hairymnstr/oggbox/sch/oggbox.sch

## KiCad design sch/oggbox.sch (2019-10-11, an earlier design)

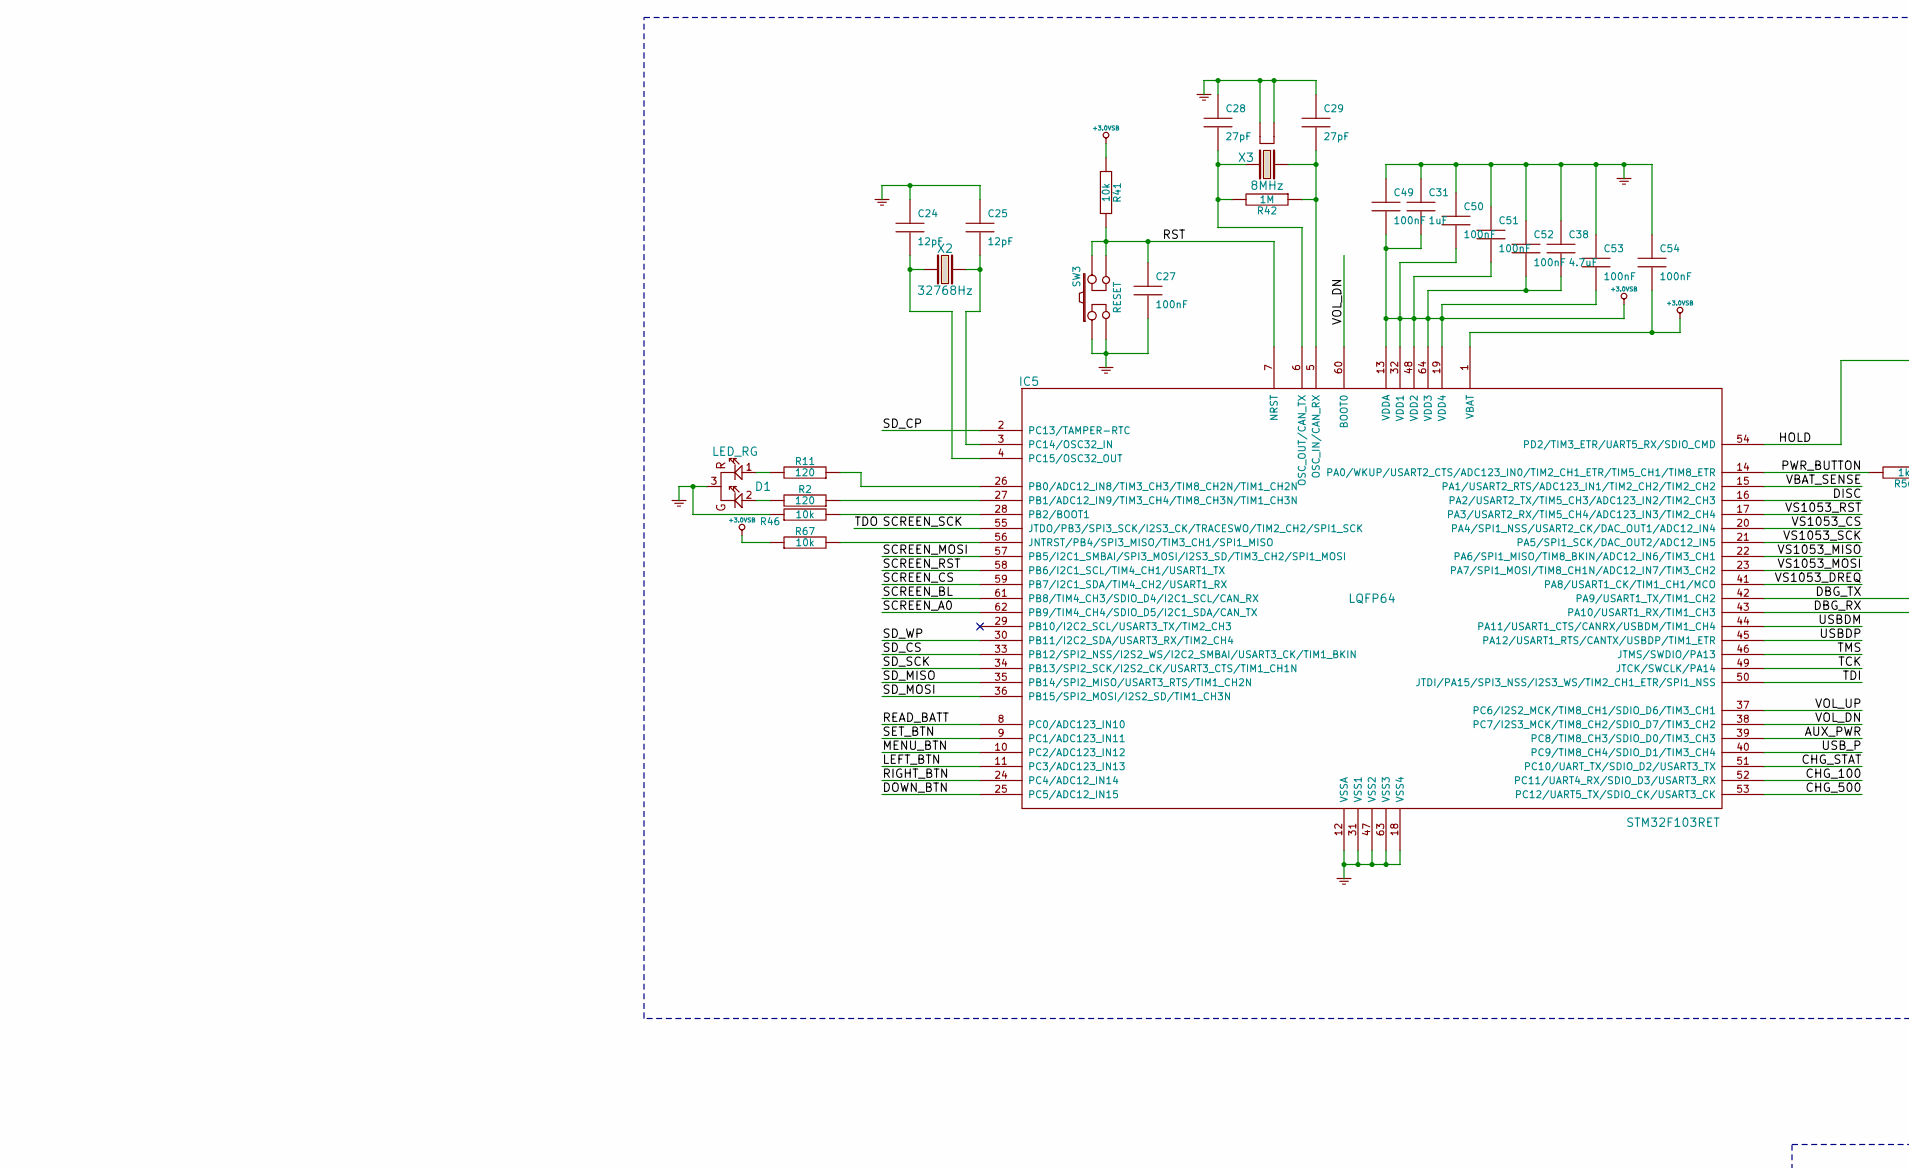
[picture p16: schematic oggbox.sch, part in row 1, column 1]



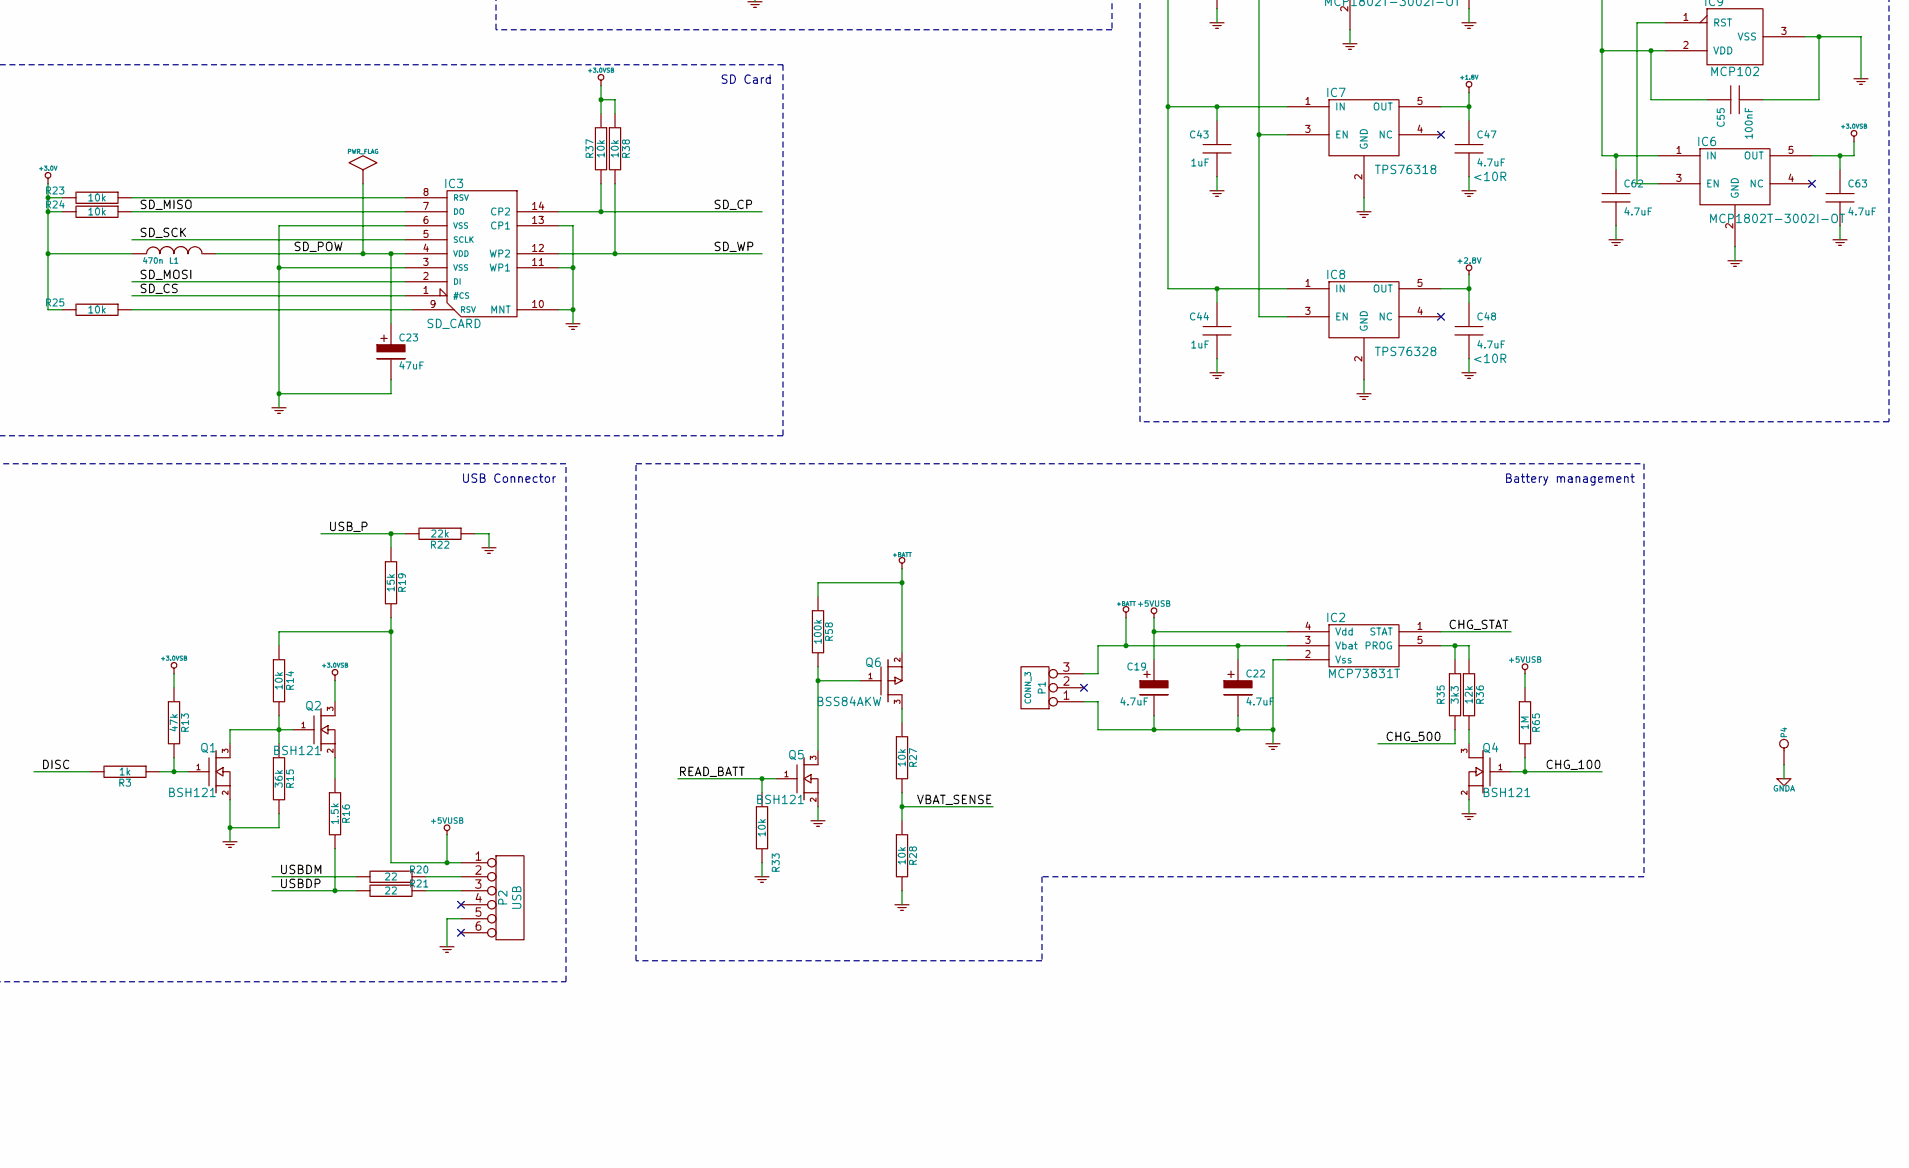
[picture p17: schematic oggbox.sch, part in row 2, column 2]

Parts:
C1, C2: 18pF; SM0603
C3, C4, C7, C31, C43, C44: 1uF; SM0603
C5, C6, C20, C21: 10nF; SM0603
C8, C9, C10, C11, C12, C13, C14, C15, C16, C17, C27, C32, C33, C34, C35, C36, C42, C45, C49, C50, C51, C52, C53, C54, C55, C56, C57, C58, C59, C60, C61: 100nF; SM0603
C18: 47nF; SM0603
C19, C22, C26, C30, C38, C47, C48, C62, C63: 4.7uF; SM0805
C23: 47uF; SM1206
C24, C25: 12pF; SM0603; Tolerance 20%; Voltage 50V
C28, C29: 27pF; SM0603
C37, C39, C40, C41: 2.2uF; SM0805
C46: 100nF; SM0603; Tolerance 20%; Voltage 50V
D1: LED_RG; SOT23
IC1: VS1053; LQFP48
IC2: MCP73831T; SOT23-5
IC3: SD_CARD; SD_UNIVERSAL
IC4, IC6: MCP1802T-3002I-OT; SOT23-5
IC5: STM32F103RET; LQFP64
IC7: TPS76318; SOT23-5
IC8: TPS76328; SOT23-5
IC9: MCP102; SOT23
L1: 470n; SM1206
P1: CONN_3; JST_S3B_XHA
P2: USB; MICRO_USB_1568026
P3: CORTEX DEBUG; SAMTEC_SHF-SM_5x2
P4: CONN_1
P5: CONN_4; BTHQ128064AVD1
P6: CONN_28; AMP_FPC_28_05MM
P7: FTDI; HEADER_6
P9: LINE; JACK_LUMBERG_1503_13_VP3
P10: PHONES; JACK_LUMBERG_1503_13_VP3
Q1, Q2, Q3, Q4, Q5: BSH121; SOT323
Q6: BSS84AKW; SOT323
R1, R4, R5, R6, R7, R8, R9, R10, R14, R23, R24, R25, R26, R27, R28, R33, R37, R38, R40, R43, R47, R55: 10k; SM0603
R2, R11: 120; SM0603; Tolerance 5%
R3, R32, R34, R44, R48, R59, R60, R61: 1k; SM0603
R12, R42, R65: 1M; SM0603
R13: 47k; SM0603
R15: 36k; SM0603
R16: 1.5k; SM0603
R17, R18: 470; SM0603
R19: 15k; SM0603
R20, R21, R29, R30, R31, R45, R53, R54: 22; SM0603
R22: 22k; SM0603
R35: 3k3; SM0603
R36: 12k; SM0603
R39: 0; SM0603
R41, R46, R67: 10k; SM0603; Tolerance 5%
R49, R50, R51, R52, R58, R62, R63, R64, R66: 100k; SM0603
R56: 1k; SM0603; Tolerance 5%
R57: 22k; SM0603; Tolerance 5%
SW1: VOL_UP; SW_SKQLLCE012
SW2: VOL_DN; SW_SKQLLCE012
SW3: RESET; SW_SKQLLCE012
SW4: MENU; SW_EVQQ2P03W
SW5: SET; SW_EVQQ2P03W
SW7: DOWN; SW_EVQQ2P03W
SW8: LEFT; SW_EVQQ2P03W
SW9: RIGHT; SW_EVQQ2P03W
SW10: UP; SW_EVQQ2P03W
SW11: HOLD; PCM12SMTR
X1: 12.288MHz; CRYSTAL-SMD-5-3_2
X2: 32768Hz; MC306
X3: 8MHz; CRYSTAL-SMD-5-3_2

Connections:
+1.8V: C14.2, C15.2, C16.2, C17.2, C47.1, IC1.5 (CVDD0), IC1.7 (CVDD1), IC1.24 (CVDD2), IC1.31 (CVDD3), IC7.5 (OUT)
+2.8V: C8.2, C9.2, C10.2, C48.1, IC1.38 (AVDD0), IC1.43 (AVDD1), IC1.45 (AVDD2), IC8.5 (OUT)
+3.0V: C11.2, C12.2, C13.2, C30.1, C42.1, C45.1, C56.1, C57.1, C58.1, C59.1, C60.1, C61.1, IC1.6 (IOVDD0), IC1.14 (IOVDD1), IC1.19 (IOVDD2), IC1.32 (XTEST), IC4.5 (OUT), L1.1, P6.15, R10.1, R23.2, R24.2, R25.2, R26.1, R53.2, R54.2, SW1.1, SW1.3, SW2.1, SW2.3, SW4.1, SW4.3, SW5.1, SW5.3, SW7.1, SW7.3, SW8.1, SW8.3, SW9.1, SW9.3
+3.0VSB: C31.2, C38.2, C49.2, C50.2, C51.2, C52.2, C53.2, C54.2, C63.1, IC5.1 (VBAT), IC5.13 (VDDA), IC5.19 (VDD4), IC5.32 (VDD1), IC5.48 (VDD2), IC5.64 (VDD3), IC6.5 (OUT), P3.1, Q2.3 (D), R13.1, R37.1, R38.1, R41.1, R67.1, SW11.1
+5VUSB: C19.1, IC2.4 (Vdd), P2.1, R14.1, R19.2, R65.1
+BATT: C22.1, C26.1, C43.1, C44.1, C55.1, C62.1, IC2.3 (Vbat), IC4.1 (IN), IC6.1 (IN), IC7.1 (IN), IC8.1 (IN), IC9.2 (VDD), P1.3, Q6.2 (S), R58.1
A1: P5.1, R53.1
A2: P5.3, R54.1
AUX_PWR: IC4.3 (EN), IC5.39 (PC8/TIM8_CH3/SDIO_D0/TIM3_CH3), IC7.3 (EN), IC8.3 (EN), R66.1
CHG_100: IC5.52 (PC11/UART4_RX/SDIO_D3/USART3_RX), Q4.1 (G), R65.2
CHG_500: IC5.53 (PC12/UART5_TX/SDIO_CK/USART3_CK), R35.2
CHG_STAT: IC2.1 (STAT), IC5.51 (PC10/UART_TX/SDIO_D2/USART3_TX)
DBG_RX: IC5.43 (PA10/USART1_RX/TIM1_CH3), P7.4
DBG_TX: IC5.42 (PA9/USART1_TX/TIM1_CH2), P7.5
DISC: IC5.16 (PA2/USART2_TX/TIM5_CH3/ADC123_IN2/TIM2_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), R3.2
DOWN_BTN: IC5.25 (PC5/ADC12_IN15), R34.1
GND: C1.2, C2.2, C11.1, C12.1, C13.1, C14.1, C15.1, C16.1, C17.1, C19.2, C22.2, C23.2, C24.1, C25.1, C26.2, C27.2, C28.1, C29.1, C30.2, C31.1, C32.2, C33.2, C34.2, C35.2, C36.2, C38.1, C41.2, C42.2, C43.2, C44.2, C47.2, C48.2, C49.1, C50.1, C51.1, C52.1, C53.1, C54.1, C55.2, C62.2, C63.2, D1.3 (GND), IC1.4 (DGND0), IC1.16 (DGND1), IC1.20 (DGND2), IC1.21 (DGND3), IC1.22 (DGND4), IC1.35 (GND), IC2.2 (Vss), IC3.3 (VSS), IC3.6 (VSS), IC3.10 (MNT), IC3.11 (WP1), IC3.13 (CP1), IC4.2 (GND), IC5.12 (VSSA), IC5.18 (VSS4), IC5.31 (VSS1), IC5.47 (VSS2), IC5.63 (VSS3), IC6.2 (GND), IC7.2 (GND), IC8.2 (GND), IC9.3 (VSS), P1.1, P2.5, P3.3, P3.5, P3.9, P6.1, P6.2, P6.14, P7.1, P7.2, Q1.2 (S), Q3.2 (S), Q4.2 (S), Q5.2 (S), R1.2, R4.2, R5.2, R6.2, R7.2, R8.2, R9.2, R15.2, R22.1, R28.2, R33.2, R39.2, R40.2, R43.2, R46.1, R47.2, R49.1, R50.2, R51.2, R52.2, R55.2, R57.1, R62.2, R63.1, R64.2, R66.2, SW3.1, SW3.3, SW11.3, SW11.4 (MECH), X1.2 (GND), X1.4 (GND), X3.2 (GND), X3.4 (GND)
GNDA: C5.1, C6.1, C7.2, C8.1, C9.1, C10.1, C18.2, C20.2, C21.2, IC1.37 (AGND0), IC1.40 (AGND1), IC1.41 (AGND2), IC1.47 (AGND3), P4.1, P9.1, R39.1
HOLD: C46.1, IC5.54 (PD2/TIM3_ETR/UART5_RX/SDIO_CMD), SW10.1, SW10.3, SW11.2
K: P5.2, P5.4, Q3.3 (D)
LEFT_BTN: IC5.11 (PC3/ADC123_IN13), R44.1
MENU_BTN: IC5.10 (PC2/ADC123_IN12), R32.1
unnamed: C1.1, IC1.17 (XTALO), R12.1, X1.1
unnamed: C2.1, IC1.18 (XTALI), R12.2, X1.3
unnamed: C3.1, R17.2
unnamed: C3.2, P9.4b
unnamed: C4.1, R18.2
unnamed: C4.2, P9.3
unnamed: C5.2, IC1.1 (MICP/LINE1), R17.1
unnamed: C6.2, IC1.48 (LINE2), R18.1
unnamed: C7.1, IC1.44 (RCAP)
unnamed: C18.1, R29.2, R45.2
unnamed: C20.1, R30.2
unnamed: C21.1, R31.2
unnamed: C24.2, IC5.4 (PC15/OSC32_OUT), X2.2
unnamed: C25.2, IC5.3 (PC14/OSC32_IN), X2.1
unnamed: C28.2, IC5.6 (OSC_OUT/CAN_TX), R42.2, X3.3
unnamed: C29.2, IC5.5 (OSC_IN/CAN_RX), R42.1, X3.1
unnamed: C32.1, P6.3
unnamed: C33.1, P6.4
unnamed: C34.1, P6.5
unnamed: C35.1, P6.6
unnamed: C36.1, P6.7
unnamed: C37.1, P6.8
unnamed: C37.2, P6.9
unnamed: C39.1, P6.10
unnamed: C39.2, C40.2, P6.11
unnamed: C40.1, P6.12
unnamed: C41.1, P6.13
unnamed: C45.2, R32.2, R49.2, SW4.2, SW4.4
unnamed: C46.2, R56.1, R57.2, SW10.4
unnamed: C56.2, R34.2, R50.1, SW7.2, SW7.4
unnamed: C57.2, R44.2, R51.1, SW8.2, SW8.4
unnamed: C58.2, R48.2, R52.1, SW9.2, SW9.4
unnamed: C59.2, R59.2, R62.1, SW5.2, SW5.4
unnamed: D1.1 (RED), R11.2
unnamed: D1.2 (GRN), R2.2
unnamed: IC1.9 (GPIO2/DCLK), R6.1
unnamed: IC1.10 (GPIO3/SDATA), R7.1
unnamed: IC1.11 (GPIO6/I2S_SCLK), R40.1
unnamed: IC1.12 (GPIO7/I2S_SDATA), R43.1
unnamed: IC1.13 (XDCS/BSYNC), R10.2
unnamed: IC1.25 (GPIO5/I2S_MCLK), R9.1
unnamed: IC1.26 (RX), R26.2
unnamed: IC1.33 (GPIO0), R4.1
unnamed: IC1.34 (GPIO1), R5.1
unnamed: IC1.36 (GPIO4/I2S_LROUT), R8.1
unnamed: IC1.39 (RIGHT), P10.3, R30.1
unnamed: IC1.42 (GBUF), P10.1, R29.1, R45.1
unnamed: IC1.46 (LEFT), P10.4a, P10.4b, R31.1
unnamed: IC2.5 (PROG), R35.1, R36.1
unnamed: IC3.8 (RSV), R23.1
unnamed: IC3.9 (RSV), R25.1
unnamed: IC5.26 (PB0/ADC12_IN8/TIM3_CH3/TIM8_CH2N/TIM1_C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), R11.1
unnamed: IC5.27 (PB1/ADC12_IN9/TIM3_CH4/TIM8_CH3N/TIM1_C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), R2.1
unnamed: IC5.28 (PB2/BOOT1), R46.2
unnamed: IC5.56 (JNTRST/PB4/SPI3_MISO/TIM3_CH1/SPI1_MISO), R67.2
unnamed: IC6.3 (EN), IC9.1 (RST)
unnamed: P2.2, R20.1
unnamed: P2.3, R21.1
unnamed: Q1.1 (G), R3.1, R13.2
unnamed: Q1.3 (D), Q2.1 (G), R14.2, R15.1
unnamed: Q2.2 (S), R16.1
unnamed: Q4.3 (D), R36.2
unnamed: Q5.3 (D), Q6.1 (G), R58.2
unnamed: Q6.3 (D), R27.1
PWR_BUTTON: IC5.14 (PA0/WKUP/USART2_CTS/ADC123_IN0/TIM2_CH1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), R56.2
READ_BATT: IC5.8 (PC0/ADC123_IN10), Q5.1 (G), R33.1
RIGHT_BTN: IC5.24 (PC4/ADC12_IN14), R48.1
RST: C27.1, IC5.7 (NRST), P3.10, R41.2, SW3.2, SW3.4
SCREEN_A0: IC5.62 (PB9/TIM4_CH4/SDIO_D5/I2C1_SDA/CAN_TX), P6.26
SCREEN_BL: IC5.61 (PB8/TIM4_CH3/SDIO_D4/I2C1_SCL/CAN_RX), Q3.1 (G), R47.1
SCREEN_CS: IC5.59 (PB7/I2C1_SDA/TIM4_CH2/USART1_RX), P6.27
SCREEN_MOSI: IC5.57 (PB5/I2C1_SMBAI/SPI3_MOSI/I2S3_SD/TIM3_C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), P6.16
SCREEN_RST: IC5.58 (PB6/I2C1_SCL/TIM4_CH1/USART1_TX), P6.28, R55.1
SCREEN_SCK: IC5.55 (JTDO/PB3/SPI3_SCK/I2S3_CK/TRACESWO/TIM2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), P3.6, P6.17
SD_CP: IC3.14 (CP2), IC5.2 (PC13/TAMPER-RTC), R37.2
SD_CS: IC3.1 (#CS), IC5.33 (PB12/SPI2_NSS/I2S2_WS/I2C2_SMBAI/USART3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)
SD_MISO: IC3.7 (DO), IC5.35 (PB14/SPI2_MISO/USART3_RTS/TIM1_CH2N), R24.1
SD_MOSI: IC3.2 (DI), IC5.36 (PB15/SPI2_MOSI/I2S2_SD/TIM1_CH3N)
SD_POW: C23.1, IC3.4 (VDD), L1.2
SD_SCK: IC3.5 (SCLK), IC5.34 (PB13/SPI2_SCK/I2S2_CK/USART3_CTS/TIM1_C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)
SD_WP: IC3.12 (WP2), IC5.30 (PB11/I2C2_SDA/USART3_RX/TIM2_CH4), R38.2
SET_BTN: IC5.9 (PC1/ADC123_IN11), R59.1
TCK: IC5.49 (JTCK/SWCLK/PA14), P3.4
TDI: IC5.50 (JTDI/PA15/SPI3_NSS/I2S3_WS/TIM2_CH1_ETR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), P3.8
TMS: IC5.46 (JTMS/SWDIO/PA13), P3.2
USBDM: IC5.44 (PA11/USART1_CTS/CANRX/USBDM/TIM1_CH4), R20.2
USBDP: IC5.45 (PA12/USART1_RTS/CANTX/USBDP/TIM1_ETR), R16.2, R21.2
USB_P: IC5.40 (PC9/TIM8_CH4/SDIO_D1/TIM3_CH4), R19.1, R22.2
VBAT_SENSE: IC5.15 (PA1/USART2_RTS/ADC123_IN1/TIM2_CH2/TIM2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), R27.2, R28.1
VDNB: C61.2, R61.1, R64.1, SW2.2, SW2.4
VOL_DN: IC5.38 (PC7/I2S3_MCK/TIM8_CH2/SDIO_D7/TIM3_CH2), IC5.60 (BOOT0), R61.2
VOL_UP: IC5.37 (PC6/I2S2_MCK/TIM8_CH1/SDIO_D6/TIM3_CH1), R60.1
VS1053_CS: IC1.23 (XCS), IC5.20 (PA4/SPI1_NSS/USART2_CK/DAC_OUT1/ADC12_I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)
VS1053_DREQ: IC1.8 (DREQ), IC5.41 (PA8/USART1_CK/TIM1_CH1/MCO)
VS1053_MISO: IC1.30 (SO), IC5.22 (PA6/SPI1_MISO/TIM8_BKIN/ADC12_IN6/TIM3_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)
VS1053_MOSI: IC1.29 (SI), IC5.23 (PA7/SPI1_MOSI/TIM8_CH1N/ADC12_IN7/TIM3_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)
VS1053_RST: IC1.3 (XRESET), IC5.17 (PA3/USART2_RX/TIM5_CH4/ADC123_IN3/TIM2_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), R1.1
VS1053_SCK: IC1.28 (SCLK), IC5.21 (PA5/SPI1_SCK/DAC_OUT2/ADC12_IN5)
VUPB: C60.2, R60.2, R63.2, SW1.2, SW1.4

Notes on the sheet:
CODEC Chip
SD Card
USB Connector
Battery management
Power Supply
Screen
Buttons
Processor
