hairymnstr/oggbox/src/firmware/ob_screen.c

#include <libopenstm32/gpio.h>
#include <libopenstm32/timer.h>
#include <libopenstm32/rcc.h>
#include "config.h"
#include "ob_screen.h"

int screen_row, screen_col, screen_inv, screen_top_row;

extern char *font[];

void ob_screen_setup() {

  rcc_peripheral_enable_clock(&RCC_APB2ENR, RCC_APB2ENR_TIM1EN);
  rcc_peripheral_enable_clock(&RCC_APB2ENR, RCC_APB2ENR_IOPAEN | RCC_APB2ENR_AFIOEN);
  rcc_peripheral_enable_clock(&RCC_APB2ENR, RCC_APB2ENR_IOPCEN);
  rcc_peripheral_enable_clock(&RCC_APB2ENR, RCC_APB2ENR_IOPDEN);
  /* === setup GPIO === */
   /* PWM output for backlight brightness */
  gpio_set_mode(SCREEN_BL_PORT, GPIO_MODE_OUTPUT_50_MHZ,
                GPIO_CNF_OUTPUT_ALTFN_PUSHPULL, SCREEN_BL);

   /* CS output for contrast control */
  gpio_set_mode(SCREEN_CON_PORT, GPIO_MODE_OUTPUT_50_MHZ,
                GPIO_CNF_OUTPUT_PUSHPULL, SCREEN_CON);
  gpio_set(SCREEN_CON_PORT, SCREEN_CON);  /* de-select this chip normally */

   /* Reset line */
  gpio_set_mode(SCREEN_RST_PORT, GPIO_MODE_OUTPUT_50_MHZ,
                GPIO_CNF_OUTPUT_PUSHPULL, SCREEN_RST);
  gpio_clear(SCREEN_RST_PORT, SCREEN_RST);    /* put chip in reset to start with */

   /* Chip selects, enable, r/w and d/i */
  gpio_set_mode(SCREEN_CS1_PORT, GPIO_MODE_OUTPUT_50_MHZ,
                GPIO_CNF_OUTPUT_PUSHPULL, SCREEN_CS1);
  gpio_set_mode(SCREEN_CS2_PORT, GPIO_MODE_OUTPUT_50_MHZ,
                GPIO_CNF_OUTPUT_PUSHPULL, SCREEN_CS2);
  gpio_set_mode(SCREEN_E_PORT, GPIO_MODE_OUTPUT_50_MHZ,
                GPIO_CNF_OUTPUT_PUSHPULL, SCREEN_E);
  gpio_set_mode(SCREEN_DI_PORT, GPIO_MODE_OUTPUT_50_MHZ,
                GPIO_CNF_OUTPUT_PUSHPULL, SCREEN_DI);
  gpio_set_mode(SCREEN_RW_PORT, GPIO_MODE_OUTPUT_50_MHZ,
                GPIO_CNF_OUTPUT_PUSHPULL, SCREEN_RW);

   /* leave the actual data bus floating for now, will set dir later */

  /* === Setup PWM peripherals for brightness === */
   /* global settings for timer 1 */
  TIM1_CR1 = TIM_CR1_CKD_CK_INT | TIM_CR1_CMS_EDGE;
  TIM1_ARR = 65535;
  TIM1_PSC = 0;
  TIM1_EGR = TIM_EGR_UG;

   /* timer 1 channel 2 (screen brightness) */
  TIM1_CCMR1 |= TIM_CCMR1_OC2M_PWM1 | TIM_CCMR1_OC2PE;
  TIM1_CCER |= TIM_CCER_CC2E;
  TIM1_CCR2 = 0;

  TIM1_CR1 |= TIM_CR1_ARPE;
  TIM1_CR1 |= TIM_CR1_CEN;

  TIM1_BDTR |= TIM_BDTR_MOE;

}

void ob_screen_set_bl(unsigned short level) {
/*  if(level > 127) {
    gpio_set(SCREEN_BL_PORT, SCREEN_BL);
  } else {
    gpio_clear(SCREEN_BL_PORT, SCREEN_BL);
  }*/

  TIM1_CCR2 = level;

  return;
}

void ob_screen_set_contrast(unsigned short level) {
  /* TODO: put a mutex to avoid interfering with screen select?? */
  int temp_cs=0;
  register int i, j;
  /* save chip selects */
  if(gpio_get(SCREEN_CS1_PORT, SCREEN_CS1)) {
    temp_cs |= 1;
    gpio_clear(SCREEN_CS1_PORT, SCREEN_CS1);
  }
  if(gpio_get(SCREEN_CS2_PORT, SCREEN_CS2)) {
    temp_cs |= 2;
    gpio_clear(SCREEN_CS2_PORT, SCREEN_CS2);
  }

  gpio_set_mode(SCREEN_DATA_PORT, GPIO_MODE_OUTPUT_50_MHZ,
                GPIO_CNF_OUTPUT_PUSHPULL, 0x3);
  
  level = (level >> 8) & 0xFF;

  level = level | 0x1100;   /* write value to pot 0 */

  gpio_clear(SCREEN_DATA_PORT, 0);    /* clock starts low */

  if(level & 0x8000) {
    gpio_set(SCREEN_DATA_PORT, 1);
  } else {
    gpio_clear(SCREEN_DATA_PORT, 1);
  }

  gpio_clear(SCREEN_CON_PORT, SCREEN_CON);  /* activate chip select */

  for(i=14;i>=0;i--) {
    for(j=0;j<5;j++);
    gpio_set(SCREEN_DATA_PORT, 0);    /* clock high, latches data */
    for(j=0;j<4;j++);
    if(level & (1 << i)) {
      gpio_set(SCREEN_DATA_PORT, 1);
    } else {
      gpio_clear(SCREEN_DATA_PORT, 1);
    }
    gpio_clear(SCREEN_DATA_PORT, 0);  /* clock low again */
  }
  /* need to put final clock pulse out, last data bit is already on the bus */
  for(j=0;j<5;j++);
  gpio_set(SCREEN_DATA_PORT, 0);
  for(j=0;j<5;j++);
  gpio_clear(SCREEN_DATA_PORT, 0);

  /* clear the CS */
  gpio_set(SCREEN_CON_PORT, SCREEN_CON);

  /* reset the data bus to input */
  gpio_set_mode(SCREEN_DATA_PORT, GPIO_MODE_INPUT,
                GPIO_CNF_INPUT_FLOAT, 0x3);

  /* replace chip select lines */
  if(temp_cs & 1) {
    gpio_set(SCREEN_CS1_PORT, SCREEN_CS1);
  }
  if(temp_cs & 2) {
    gpio_set(SCREEN_CS2_PORT, SCREEN_CS2);
  }
    
  return;
}

void ob_screen_instruction(unsigned char code, unsigned char val) {
  int i, t;

  /* instruction mode */
  gpio_clear(SCREEN_DI_PORT, SCREEN_DI);
  /* read mode */
  gpio_set(SCREEN_RW_PORT, SCREEN_RW);
  
  /* wait for screen to be ready */
  do {
    for(i=0;i<WAIT;i++);
    gpio_set(SCREEN_E_PORT, SCREEN_E);
    for(i=0;i<WAIT;i++);
    t = SCREEN_DATA_IN & 0x80;     /* mask for the busy flag */
    gpio_clear(SCREEN_E_PORT, SCREEN_E);
  } while(t);

  /* set write mode */
  gpio_clear(SCREEN_RW_PORT, SCREEN_RW);

  /* set the data bus to write */
  gpio_set_mode(SCREEN_DATA_PORT, GPIO_MODE_OUTPUT_50_MHZ,
                GPIO_CNF_OUTPUT_PUSHPULL, 0xFF);

  for(i=0;i<WAIT;i++);

  SCREEN_DATA_OUT = (SCREEN_DATA_OUT & 0xFF00) | code | val;

  for(i=0;i<WAIT;i++);
  gpio_set(SCREEN_E_PORT, SCREEN_E);
  for(i=0;i<WAIT;i++);
  gpio_clear(SCREEN_E_PORT, SCREEN_E);

  for(i=0;i<WAIT;i++);
  /* set the data bus back to input only */
  gpio_set_mode(SCREEN_DATA_PORT, GPIO_MODE_INPUT,
                GPIO_CNF_INPUT_FLOAT, 0xFF);

  return;
}

void ob_screen_data(unsigned char val) {
  int i, t;

  /* instruction mode */
  gpio_clear(SCREEN_DI_PORT, SCREEN_DI);
  /* read mode */
  gpio_set(SCREEN_RW_PORT, SCREEN_RW);
  
  //ob_printf("checking screen status\n");

  /* wait for screen to be ready */
  do {
    for(i=0;i<WAIT;i++);
    gpio_set(SCREEN_E_PORT, SCREEN_E);
    for(i=0;i<WAIT;i++);
    t = SCREEN_DATA_IN & 0x80;     /* mask for the busy flag */
    //ob_printf("data is %x\n", SCREEN_DATA_IN);
    gpio_clear(SCREEN_E_PORT, SCREEN_E);
  } while(t);

  //ob_printf("okay, writing data\n");

  /* set write mode */
  gpio_clear(SCREEN_RW_PORT, SCREEN_RW);
  /* data mode */
  gpio_set(SCREEN_DI_PORT, SCREEN_DI);

  /* set the data bus to write */
  gpio_set_mode(SCREEN_DATA_PORT, GPIO_MODE_OUTPUT_50_MHZ,
                GPIO_CNF_OUTPUT_PUSHPULL, 0xFF);

  for(i=0;i<WAIT;i++);

  SCREEN_DATA_OUT = (SCREEN_DATA_OUT & 0xFF00) | val;

  for(i=0;i<WAIT;i++);
  gpio_set(SCREEN_E_PORT, SCREEN_E);
  for(i=0;i<WAIT;i++);
  gpio_clear(SCREEN_E_PORT, SCREEN_E);

  for(i=0;i<WAIT;i++);
  /* set the data bus back to input only */
  gpio_set_mode(SCREEN_DATA_PORT, GPIO_MODE_INPUT,
                GPIO_CNF_INPUT_FLOAT, 0xFF);

  return;
}

void ob_screen_startup() {
  int i;

  gpio_clear(SCREEN_RST_PORT, SCREEN_RST);

  for(i=0;i<10000;i++);

  gpio_clear(SCREEN_E_PORT, SCREEN_E);
  gpio_clear(SCREEN_CS1_PORT, SCREEN_CS1);
  gpio_clear(SCREEN_CS2_PORT, SCREEN_CS2);
  gpio_set(SCREEN_DI_PORT, SCREEN_DI);
  gpio_set(SCREEN_RW_PORT, SCREEN_RW);
  gpio_set(SCREEN_RST_PORT, SCREEN_RST);

  for(i=0;i<10000;i++);

  gpio_set(SCREEN_CS1_PORT, SCREEN_CS1);
  //gpio_clear(SCREEN_CS2_PORT, SCREEN_CS2);


//  ob_printf("setting screen on\n");
  ob_screen_instruction(SCREEN_ON, 0);
//  ob_printf("setting screen col=0\n");
  ob_screen_instruction(SCREEN_COL, 0);
//  ob_printf("setting screen row=0\n");
  ob_screen_instruction(SCREEN_ROW, 0);

  gpio_clear(SCREEN_CS1_PORT, SCREEN_CS1);
  gpio_set(SCREEN_CS2_PORT, SCREEN_CS2);

  ob_screen_instruction(SCREEN_ON, 0);
  ob_screen_instruction(SCREEN_COL, 0);
  ob_screen_instruction(SCREEN_ROW, 0);

  screen_row = 0;
  screen_col = 0;
  screen_top_row = 0;
  screen_inv = 0;

//  ob_printf("clearing screen \n");

  ob_screen_clear();
  return;
}

void ob_screen_test() {
  int i;

  gpio_set(SCREEN_CS1_PORT, SCREEN_CS1);
  gpio_clear(SCREEN_CS2_PORT, SCREEN_CS2);

  for(i=0;i<10000;i++);

//  ob_printf("byte 0\n");
  ob_screen_data(0xAA);
//  ob_printf("byte 1\n");
  ob_screen_data(0x55);
//  ob_printf("byte 2\n");
  ob_screen_data(0xFF);

  return;
}

void ob_screen_clear_row(int row) {
  register int i;
  ob_screen_set_row(row);
  gpio_set(SCREEN_CS1_PORT, SCREEN_CS1);
  gpio_clear(SCREEN_CS2_PORT, SCREEN_CS2);
  for(i=0;i<64;i++) {
    if(screen_inv) {
      ob_screen_data(0xFF);
    } else {
      ob_screen_data(0x00);
    }
  }
  gpio_set(SCREEN_CS2_PORT, SCREEN_CS2);
  gpio_clear(SCREEN_CS1_PORT, SCREEN_CS1);
  for(i=0;i<64;i++) {
    if(screen_inv) {
      ob_screen_data(0xFF);
    } else {
      ob_screen_data(0x00);
    }
  }
}

void ob_screen_clear() {
  register int i;
  for(i=0;i<8;i++) {
    ob_screen_clear_row(i);
  }
  ob_screen_set_row(0);
}

int ob_screen_print(char *s) {
  char *cp = s;
  register int i;

  while((*cp) != 0) {
    if((screen_col < 21) && ((*cp) != '\n')) {
      for(i=0;i<6;i++) {
        if((screen_col * 6 + i) >= 64) {
          gpio_clear(SCREEN_CS1_PORT, SCREEN_CS1);
          gpio_set(SCREEN_CS2_PORT, SCREEN_CS2);
        } else {
          gpio_set(SCREEN_CS1_PORT, SCREEN_CS1);
          gpio_clear(SCREEN_CS2_PORT, SCREEN_CS2);
        }
        if(screen_inv) {
          ob_screen_data(font[(*cp)][i] ^ 0xFF);
        } else {
          ob_screen_data(font[(*cp)][i]);
        }
      }
      screen_col++;
      cp++;
    } else {
      break;
    }
  }
  return (int)(s - cp);
}

int ob_screen_get_row() {
  return screen_row;
}

int ob_screen_get_col() {
  return screen_col;
}

void ob_screen_set_row(int row) {
  row = row % 8;
  screen_row = row;
  row = (row + screen_top_row) % 8;

  gpio_set(SCREEN_CS1_PORT, SCREEN_CS1);
  gpio_clear(SCREEN_CS2_PORT, SCREEN_CS2);
  ob_screen_instruction(SCREEN_ROW, row);
  ob_screen_instruction(SCREEN_COL, 0);

  gpio_clear(SCREEN_CS1_PORT, SCREEN_CS1);
  gpio_set(SCREEN_CS2_PORT, SCREEN_CS2);
  ob_screen_instruction(SCREEN_ROW, row);
  ob_screen_instruction(SCREEN_COL, 0);
}

void ob_screen_set_col(int col) {
  col = col % 21;
  screen_col = col;
  col = col * 6;
  if(col < 64) {
    gpio_set(SCREEN_CS1_PORT, SCREEN_CS1);
    gpio_clear(SCREEN_CS2_PORT, SCREEN_CS2);
    ob_screen_instruction(SCREEN_COL, col);
    col = 0;
  } else {
    col = col - 64;
  }
  gpio_clear(SCREEN_CS1_PORT, SCREEN_CS1);
  gpio_set(SCREEN_CS2_PORT, SCREEN_CS2);
  ob_screen_instruction(SCREEN_COL, col);
}

void ob_screen_set_inv(int yes) {
  if(yes) {
    screen_inv = SCREEN_INV;
  } else {
    screen_inv = SCREEN_NORM;
  }
}

int ob_screen_get_inv() {
  return (screen_inv == SCREEN_INV);
}
