hairymnstr/oggbox/firmware/src/interface.c

#include <libopencm3/stm32/gpio.h>

#include <stdio.h>
#include <string.h>

#include "FreeRTOS.h"
#include "task.h"
#include "queue.h"

#include "vs1053.h"
#include "screen.h"
#include "power.h"
#include "usb.h"
#include "interface.h"
#include "config.h"

#define INTERFACE_TASK_STACK_SIZE 1024
#define INTERFACE_TASK_PRIORITY (tskIDLE_PRIORITY + 1)

extern xQueueHandle player_queue;
int _display_mode;

void set_display_mode(int mode) {
  static int last_mode = DISPLAY_MODE_NOW_PLAYING;
  int temp;
  
  if(mode == DISPLAY_MODE_PREVIOUS) {
    temp = last_mode;
    last_mode = _display_mode;
    _display_mode = temp;
  } else {
    last_mode = _display_mode;
    _display_mode = mode;
  }
}

int get_display_mode() {
  return _display_mode;
}
  
// Now playing screen, shows title, artist and progress
void interface_now_playing(int buttons) {
  char *msg;
  static int artist_dir = -1;
  static int artist_index = 0;
  static int title_dir = -1;
  static int title_index = 0;
  static int album_dir = -1;
  static int album_index = 0;
  char buf[12];
  
  if(player_is_playing()) {
    msg = player_get_artist();
    frame_print_at(artist_index,24,msg);
    if(strlen(msg) > 10) {
      // need to scroll the artist name
      if(artist_dir == 1) {
        if(artist_index == 0) {
          artist_dir = -10;
        } else {
          artist_index += artist_dir;
        }
      } else if(artist_dir == -1) {
        if(artist_index == (((int)strlen(msg) * -6) + 64)) {
          artist_dir = 10;
        } else {
          artist_index += artist_dir;
        }
      } else {
        if(artist_dir > 0) {
          artist_dir --;
        } else {
          artist_dir ++;
        }
      }
    } else {
      artist_index = 0;
    }
    
    msg = player_get_title();
    frame_print_at(title_index,32,msg);
    if(strlen(msg) > 10) {
      // need to scroll the artist name
      if(title_dir == 1) {
        if(title_index == 0) {
          title_dir = -10;
        } else {
          title_index += title_dir;
        }
      } else if(title_dir == -1) {
        if(title_index == (((int)strlen(msg) * -6) + 64)) {
          title_dir = 10;
        } else {
          title_index += title_dir;
        }
      } else {
        if(title_dir > 0) {
          title_dir --;
        } else {
          title_dir ++;
        }
      }
    } else {
      title_index = 0;
    }
    
    msg = player_get_album();
    frame_print_at(album_index,40,msg);
    if(strlen(msg) > 10) {
      // need to scroll the artist name
      if(album_dir == 1) {
        if(album_index == 0) {
          album_dir = -10;
        } else {
          album_index += album_dir;
        }
      } else if(album_dir == -1) {
        if(album_index == (((int)strlen(msg) * -6) + 64)) {
          album_dir = 10;
        } else {
          album_index += album_dir;
        }
      } else {
        if(album_dir > 0) {
          album_dir --;
        } else {
          album_dir ++;
        }
      }
    } else {
      album_index = 0;
    }
    
    sniprintf(buf, sizeof(buf), "%3lu%%", (100 * player_get_position()) / player_get_length());
    frame_print_at(12,56,buf);
  }
  
  if(buttons & MENU_BTN_FLAG) {
    set_display_mode(DISPLAY_MODE_MENU);
  }
}

void interface_main_menu(int buttons) {
  static int option = 0;
  int option_count = 4;
  
  frame_print_at(5, 16, "Now");
  frame_print_at(10, 24, "Playing");
  frame_print_at(5, 36, "Playlist");
  frame_print_at(5, 52, "Media");
  frame_print_at(5, 68, "Settings");
  
  frame_draw_rect(0,(option + 1) * 16,64,16,FILL_TYPE_INVERT, FILL_TYPE_INVERT);
  
  if(buttons & DOWN_BTN_FLAG) {
    option = (option + 1) % option_count;
  } else if(buttons & UP_BTN_FLAG) {
    if(option > 0) {
      option --;
    } else {
      option = option_count-1;
    }
  } else if(buttons & MENU_BTN_FLAG) {
    option = 0;
    set_display_mode(DISPLAY_MODE_PREVIOUS);
  } else if(buttons & RIGHT_BTN_FLAG) {
    // dispatch to next layer down
    if(option == 0) {
      set_display_mode(DISPLAY_MODE_NOW_PLAYING);
    } else if(option == 1) {
      set_display_mode(DISPLAY_MODE_PLAYLIST);
    } else if(option == 2) {
      set_display_mode(DISPLAY_MODE_MEDIA);
    } else if(option == 3) {
      set_display_mode(DISPLAY_MODE_SETTINGS);
    }
  }
}

void interface_playlist(int buttons) {
  if(buttons & MENU_BTN_FLAG) {
    set_display_mode(DISPLAY_MODE_MENU);
  }
}

void interface_media(int buttons) {
  if(buttons & MENU_BTN_FLAG) {
    set_display_mode(DISPLAY_MODE_MENU);
  }
}

void interface_settings(int buttons) {
  
  if(buttons & MENU_BTN_FLAG) {
    set_display_mode(DISPLAY_MODE_MENU);
  }
}

int check_buttons() {
  int buttons = 0;
  
  if(gpio_get(VOL_UP_PORT, VOL_UP_PIN)) {
    buttons |= VOL_UP_BTN_FLAG;
  }
  if(gpio_get(VOL_DOWN_PORT, VOL_DOWN_PIN)) {
    buttons |= VOL_DN_BTN_FLAG;
  }
  if(gpio_get(MENU_BTN_PORT, MENU_BTN_PIN)) {
    buttons |= MENU_BTN_FLAG;
  }
  if(gpio_get(SET_BTN_PORT, SET_BTN_PIN)) {
    buttons |= SET_BTN_FLAG;
  }
  if(gpio_get(UP_BTN_PORT, UP_BTN_PIN)) {
    buttons |= UP_BTN_FLAG;
  }
  if(gpio_get(DOWN_BTN_PORT, DOWN_BTN_PIN)) {
    buttons |= DOWN_BTN_FLAG;
  }
  if(gpio_get(LEFT_BTN_PORT, LEFT_BTN_PIN)) {
    buttons |= LEFT_BTN_FLAG;
  }
  if(gpio_get(RIGHT_BTN_PORT, RIGHT_BTN_PIN)) {
    buttons |= RIGHT_BTN_FLAG;
  }
  return buttons;
}

static void interface_task(void *parameter __attribute__((unused))) {
  int volume = 16;
  char msg[30];
  int buttons;
  int mode;
  struct player_job player_job_to_do;
  uint32_t last_ui_update=0;
  uint32_t off_timer = 0;
  
  screen_init();
  
  screen_backlight(65535);
  
  // set display mode twice so that the previous mode
  // is set as well
  set_display_mode(DISPLAY_MODE_NOW_PLAYING);
  set_display_mode(DISPLAY_MODE_NOW_PLAYING);
  while(1) {
    
    buttons = check_buttons();
    
    // check for press & hold on up button to power off
    if(buttons & UP_BTN_FLAG) {
      if(xTaskGetTickCount() - off_timer > 3000) {
        power_sleep();
      }
    } else {
      off_timer = xTaskGetTickCount();
    }
    
    if(xTaskGetTickCount() - last_ui_update >= 100) {
      iprintf("Screen update\r\n");      
      if(buttons & VOL_UP_BTN_FLAG) {
        if(volume > 0)
          volume--;
        player_job_to_do.type = PLAYER_VOLUME_COMMAND;
        player_job_to_do.data = volume | (volume << 8);
        xQueueSendToBack(player_queue, &player_job_to_do, 0);
      }
      if(buttons & VOL_DN_BTN_FLAG) {
        if(volume < 0xFD)
          volume++;
        player_job_to_do.type = PLAYER_VOLUME_COMMAND;
        player_job_to_do.data = volume | (volume << 8);
        xQueueSendToBack(player_queue, &player_job_to_do, 0);
      }
      // update the screen
      
      frame_clear();
      
      if(usb_get_status() == USB_STATUS_ACTIVE) {
        frame_print_at(20, 100, "data");
      } else if(usb_get_status() == USB_STATUS_CHARGER) {
        frame_print_at(11, 100, "charger");
      }
        
      
      sniprintf(msg, 10, "%3d.%ddB", -1 * (volume / 2), ((volume & 1) * 5));
      frame_print_at(8, 112,msg);
      sniprintf(msg, 10, "%d.%03dV", power_latest_battery() / 1000, power_latest_battery() % 1000);
      frame_print_at(14,120,msg);
      
      mode = get_display_mode();
      if(mode == DISPLAY_MODE_NOW_PLAYING) {
        interface_now_playing(buttons);
      } else if(mode == DISPLAY_MODE_MENU) {
        interface_main_menu(buttons);
      } else if(mode == DISPLAY_MODE_MEDIA) {
        interface_media(buttons);
      } else if(mode == DISPLAY_MODE_PLAYLIST) {
        interface_playlist(buttons);
      } else if(mode == DISPLAY_MODE_SETTINGS) {
        interface_settings(buttons);
      }
      frame_show();
      last_ui_update = xTaskGetTickCount();
    }
      
  }
  configASSERT(0);
  // interface loop shouldn't exit
}

void start_interface_task() {
    configASSERT(xTaskCreate(interface_task, "INTERFACE", INTERFACE_TASK_STACK_SIZE, NULL, INTERFACE_TASK_PRIORITY, NULL) == pdPASS);
}
