hairymnstr/oggbox/src/firmware/meta_db.c

#include <stdio.h>
#include <stdlib.h>
#include <stdint.h>
#include <string.h>

#include "meta_db.h"

// int meta_db_init() {
//   return 0;
// }
// 
// int meta_db_get_artist_byid(int id, struct artist *result) {
// 
// }
// 
// int meta_db_get_artist_byname(char *name, struct artist *result) {
// 
// }
// 
// int meta_db_get_track_byid(int id, struct track *result) {
// 
// }
// 
// int meta_db_get_album_byname(char *name, struct album *result) {
//   struct db_context context;
// 
//   context.record = 0;
// 
//   while(meta_db_next_album(result, &context)) {
//     if(strcmp(temp.title, name) == 0) {
//       return 1;
//     }
//   }
//   return 0;
// }
// 
// int meta_db_next_album(struct album *result, struct db_context *context) {
//   if(context->record >= db_global.album_record_count) {
//     return 0;
//   }
//   fseek(db_global.dbf, db_global.album_data_start + (context->record * sizeof(struct album)), SEEK_SET);
//   if(fread(result, sizeof(struct album), 1, db_global.dbf) < sizeof(struct album)) {
//     return 0;
//   }
//   return 1;
// }
// 
// int meta_db_insert_album(struct album *record) {
//   
// }

uint64_t meta_db_string_hash(char *input) {
  uint64_t hash = 0;
  char temp[8];
  int i;
  strncpy(temp, input, 8);
  for(i=0;i<8;i++) {
    if((temp[i] >= 'a') && (temp[i] <= 'z')) {
      temp[i] -= ('a' - 'A');
    }
  }
  if(strcmp(temp, "THE ") == 0) {
    return meta_db_string_hash(&input[4]);
  }
  
  for(i=0;i<8;i++) {
    hash += (temp[i] << (8 * (7-i)));
  }
  return hash;
}

/*************************************************************************************************/
/* Generic B-Tree database with minimal memory footprint functions below                         */
/*************************************************************************************************/

void meta_db_init(struct db_context *c) {
  c->head = (Node *)malloc(sizeof(Node));
  c->head->pointers_len = 0;
  c->head->keys_len = 0;
  c->head->parent = NULL;
  c->head->isleaf = -1;
  c->head->leftmost = -1;
  c->head->minval = -1;
  c->size = 0;
}

void pointer_shift(int src_pos, void *src[], int dst_pos, void *dst[], int count) {
  while(count > 0) {
    dst[count + dst_pos - 1] = src[count + src_pos - 1];
    count--;
  }
}

void keys_shift(int src_pos, uint64_t *src, int dst_pos, uint64_t *dst, int count) {
  while(count > 0) {
    dst[count + dst_pos - 1] = src[count + src_pos - 1];
    count--;
  }
}

int meta_db_insert(void *ptr, uint64_t key, Node *n, int isdata, struct db_context *context) {
  int i;
  Node *sibling;
  /* The b tree needs initialising with at least the first two entries.  Since we don't have
     lots of RAM to do an initial bulk insert, we'll put two exceptions in this function in ROM. */
  if(context->size == 0) {
    n->pointers[0] = ptr;
    n->pointers_len = 1;
    n->keys[0] = key;
    n->keys_len = 1;
    context->size++;
    return 0;
  } else if(context->size == 1) {
    if(n->keys[0] > key) {
      n->pointers[1] = n->pointers[0];
      n->pointers[0] = ptr;
      n->pointers_len = 2;
      n->minval = key;
    } else {
      n->minval = n->keys[0];
      n->keys[0] = key;
      n->pointers[1] = ptr;
      n->pointers_len = 2;
    }
    context->size++;
    return 0;
  } else {
    i = 0;
    while(i < n->keys_len) {
      if(n->keys[i] < key)
        i++;
      else
        break;
    }
    
    if(isdata && (!n->isleaf)) {
      meta_db_insert(ptr, key, n->pointers[i], isdata, context);
      return 0;
    } else {
      if(n->keys_len < METADB_NODE_SIZE) {
        if(!isdata) {
          ((Node *)ptr)->parent = n;
        }
        if(n->leftmost && (key < n->minval)) {
          pointer_shift(0, n->pointers, 1, n->pointers, n->pointers_len);
          n->pointers[0] = ptr;
          n->pointers_len++;
          keys_shift(0, n->keys, 1, n->keys, n->keys_len);
          n->keys[0] = n->minval;
          n->keys_len++;
          n->minval = key;
        } else {
          pointer_shift(i+1, n->pointers, i+2, n->pointers, n->pointers_len - i - 1);
          n->pointers[i+1] = ptr;
          n->pointers_len++;
          keys_shift(i, n->keys, i+1, n->keys, n->keys_len - i);
          n->keys[i] = key;
          n->keys_len++;
        }
        if(isdata) {
          context->size++;
        }
        return 0;
      } else {
        /* One whole node is full.  This code implements splitting the current node in two
           Once done it calls this function again searching the tree from the parent of the two
           new nodes to insert the actual data now we know there's room */
        sibling = (Node *)malloc(sizeof(Node));
        pointer_shift(METADB_MID_PTR, n->pointers, 0, sibling->pointers, METADB_MID_PTR);
        sibling->pointers_len = METADB_MID_PTR;
        sibling->isleaf = n->isleaf;    // if this is a leaf the new sibling will be
        if(!sibling->isleaf) {
          for(i=0;i<sibling->pointers_len;i++) {
            ((Node *)sibling->pointers[i])->parent = sibling;
          }
        }
        keys_shift(METADB_2ND_KEY, n->keys, 0, sibling->keys, METADB_KEY_COUNT);
        sibling->keys_len = METADB_KEY_COUNT;
        sibling->leftmost = 0;
        if(n->parent == NULL) {
          // this was the root node that's just been split.  We need to make a new root
          n->parent = (Node *)malloc(sizeof(Node));
          n->parent->parent = NULL;
          n->parent->isleaf = 0;
          n->parent->leftmost = 0;
          n->parent->pointers[0] = n;
          sibling->parent = n->parent;
          n->parent->pointers[1] = sibling;
          n->parent->pointers_len = 2;
          n->parent->keys[0] = n->keys[METADB_PASS_KEY];
          n->parent->keys_len = 1;
          n->parent->minval = n->minval;
          context->head = n->parent;
        } else {
          meta_db_insert(sibling, n->keys[METADB_PASS_KEY], n->parent, 0, context);
        }
        
        n->pointers_len = METADB_MID_PTR;
        n->keys_len = METADB_KEY_COUNT;
        
        // Finally this is where we ask it to try and insert this record again
        meta_db_insert(ptr, key, n->parent, isdata, context);
      }
    }
  }
  return 0;
}

// uint32_t meta_db_allocate_block(struct db_context *context) {
//   return context->next_block++;
// }
