hairymnstr/oggbox/src/firmware/icons.c

#include <stdint.h>

const uint8_t *sdpresentimg = "\x00\x3c\x24\x24\x24\x24\x1c\x00";
const uint8_t *sdabsentimg = "\x01\x3e\x24\x2c\x34\x24\x5c\x80";
const uint8_t *lockedimg = "\x00\x18\x24\x24\x7e\x66\x7e\x00";
const uint8_t *unlockedimg = "\x00\x18\x04\x04\x7e\x66\x7e\x00";
