hairymnstr/oggbox/src/firmware/icons.h

#ifndef ICONS_H
#define ICONS_H 1

#include <stdint.h>

extern const uint8_t *sdpresentimg;
extern const uint8_t *sdabsentimg;
extern const uint8_t *lockedimg;
extern const uint8_t *unlockedimg;
#endif /* ifndef ICONS_H */
